razanhmede/Sorting_Conveyer_Belt_System/MEE341 - Project Submission/MEE341 - Project Submission/Mechanical Design 2/Gripper Assembly.SLDASM

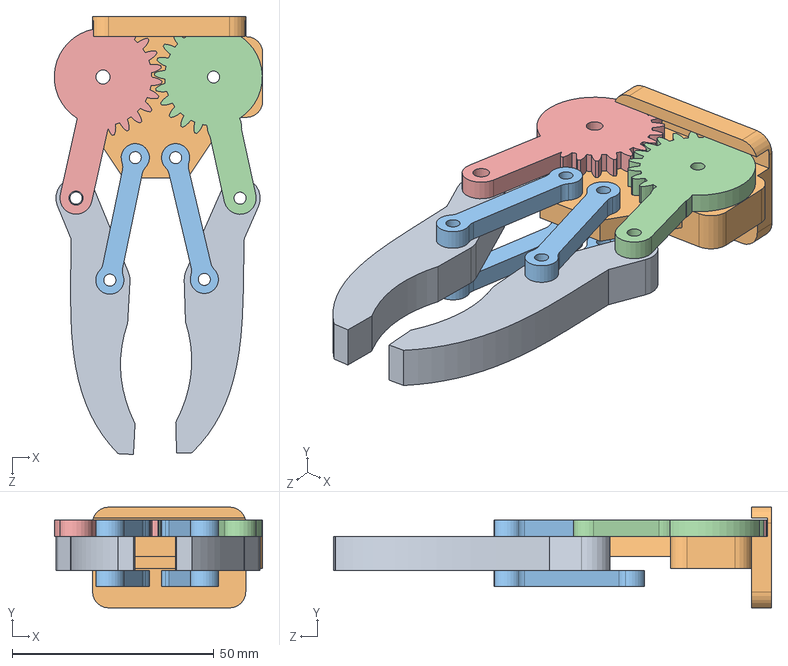
[picture p17: CAD file, 2024-09-03]
MEE341 - Project Submission/MEE341 - Project Submission/Mechanical Design 2/Gripper Assembly.SLDASM
51.7 x 25.0 x 108.6 mm
gear1
gear2
grip link 1 x 4
Gripper Base
Gripper 1 x 2
