razanhmede/Sorting_Conveyer_Belt_System/MEE341 - Project Submission/MEE341 - Project Submission/Mechanical Design 2/Robotic Arm Assembly.SLDASM

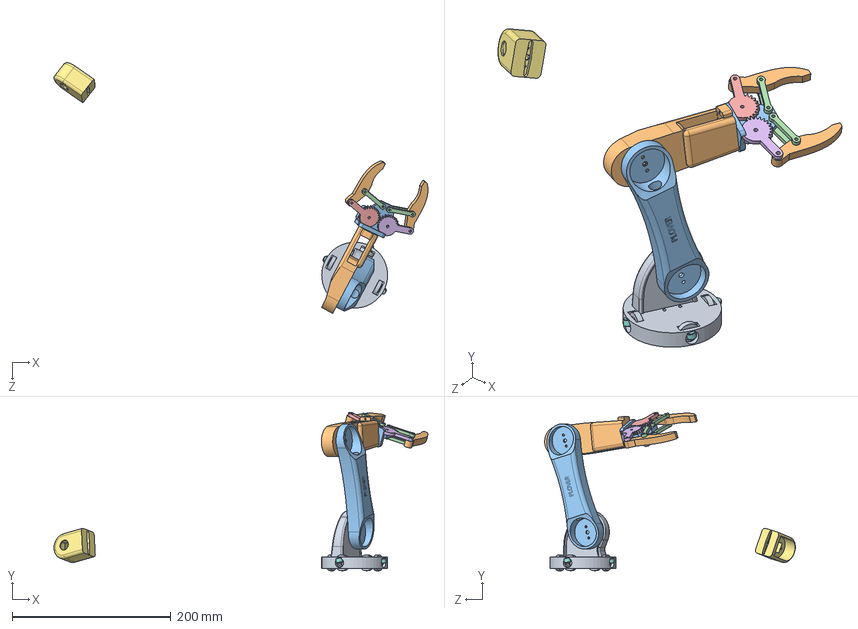
[picture p18: CAD file, 2024-09-03]
MEE341 - Project Submission/MEE341 - Project Submission/Mechanical Design 2/Robotic Arm Assembly.SLDASM
470.7 x 199.5 x 315.6 mm
Link 1
Link 2
Bearing x 4
Pin x 4
Link 3
gear1
gear2
grip link 1 x 4
Gripper Base
Gripper 1 x 2
Base Link - Copy
