razanhmede/Sorting_Conveyer_Belt_System/MEE341 - Project Submission/MEE341 - Project Submission/Mechanical Design 1/Pin.SLDPRT

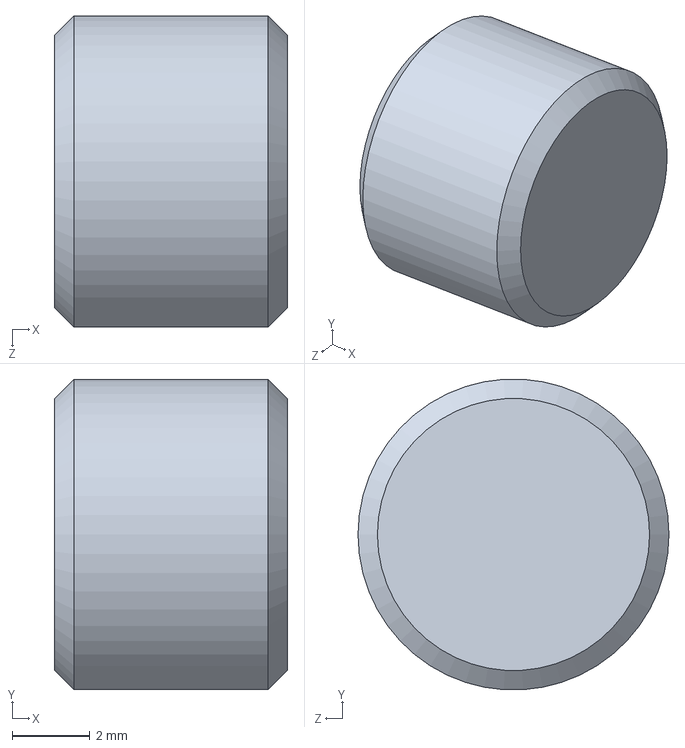
[picture p32: CAD file, 2024-09-03]
MEE341 - Project Submission/MEE341 - Project Submission/Mechanical Design 1/Pin.SLDPRT
6.00 x 7.98 x 8.00 mm
