razanhmede/Sorting_Conveyer_Belt_System/MEE341 - Project Submission/MEE341 - Project Submission/Mechanical Design 2/grip link 1_r1.SLDPRT

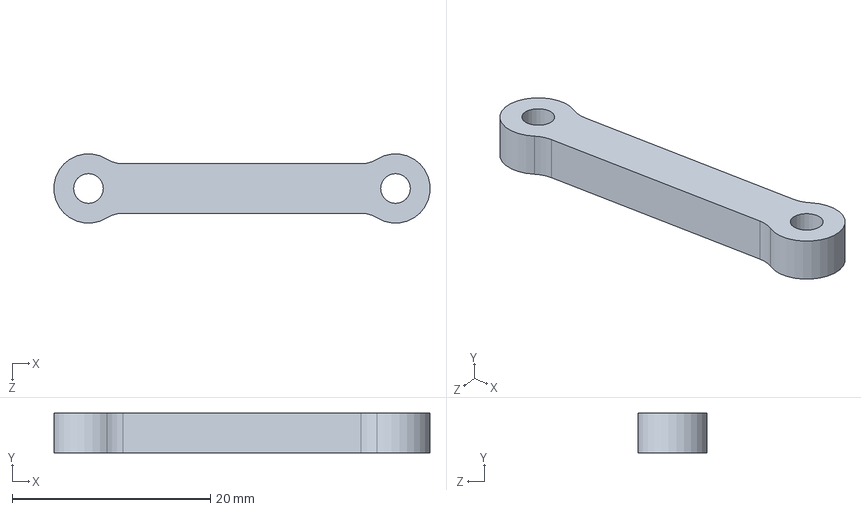
[picture p33: CAD file, 2024-09-03]
MEE341 - Project Submission/MEE341 - Project Submission/Mechanical Design 2/grip link 1_r1.SLDPRT
38.0 x 4.00 x 6.96 mm
