razanhmede/Sorting_Conveyer_Belt_System/MEE341 - Project Submission/MEE341 - Project Submission/Mechanical Design 1/Spacer.SLDPRT

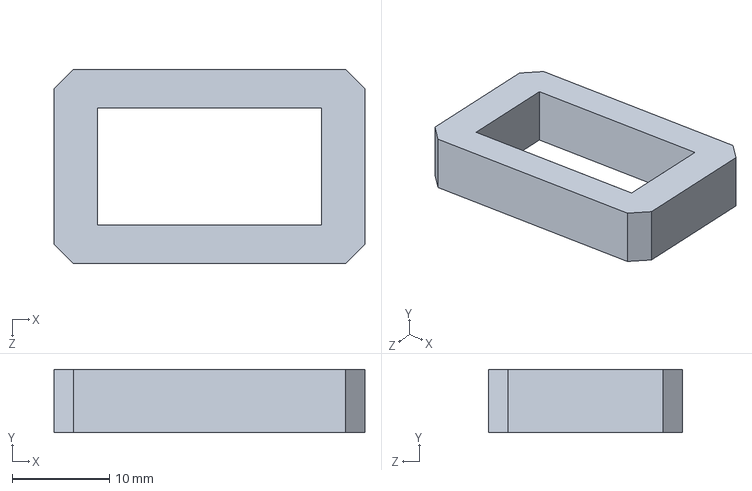
[picture p34: CAD file, 2024-09-03]
MEE341 - Project Submission/MEE341 - Project Submission/Mechanical Design 1/Spacer.SLDPRT
32.0 x 6.50 x 20.0 mm
