razanhmede/Sorting_Conveyer_Belt_System/MEE341 - Project Submission/MEE341 - Project Submission/Mechanical Design 1/spacer.STL.SLDPRT

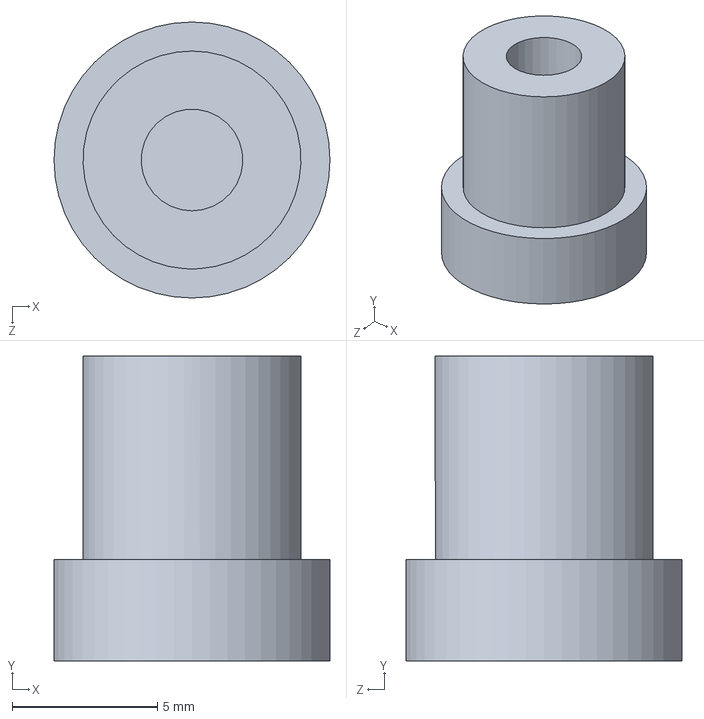
[picture p35: CAD file, 2024-09-03]
MEE341 - Project Submission/MEE341 - Project Submission/Mechanical Design 1/spacer.STL.SLDPRT
9.50 x 10.5 x 9.50 mm
