razanhmede/Sorting_Conveyer_Belt_System/MEE341 - Project Submission/MEE341 - Project Submission/Mechanical Design 2/Gripper 1.SLDPRT

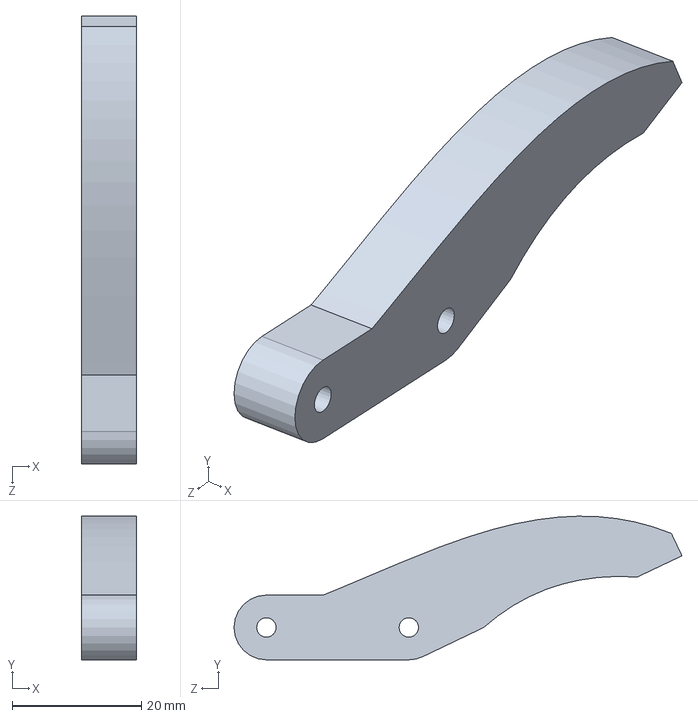
[picture p36: CAD file, 2024-09-03]
MEE341 - Project Submission/MEE341 - Project Submission/Mechanical Design 2/Gripper 1.SLDPRT
8.50 x 22.2 x 69.2 mm
