razanhmede/Sorting_Conveyer_Belt_System/MEE341 - Project Submission/MEE341 - Project Submission/Mechanical Design 2/Pin.SLDPRT

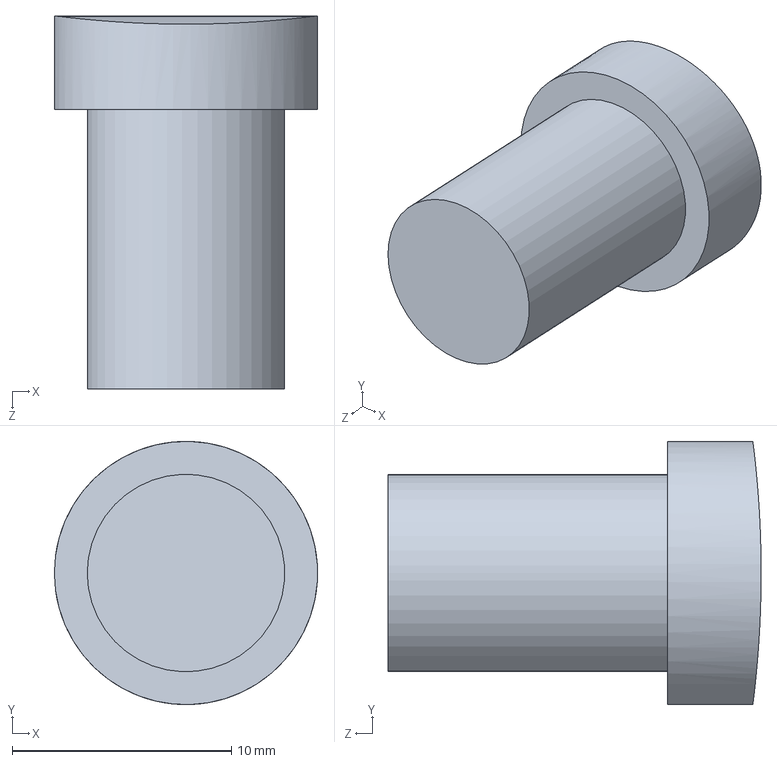
[picture p37: CAD file, 2024-09-03]
MEE341 - Project Submission/MEE341 - Project Submission/Mechanical Design 2/Pin.SLDPRT
12.0 x 12.0 x 17.0 mm
