razanhmede/Sorting_Conveyer_Belt_System/MEE341 - Project Submission/MEE341 - Project Submission/Mechanical Design 2/Gripper Base.SLDPRT

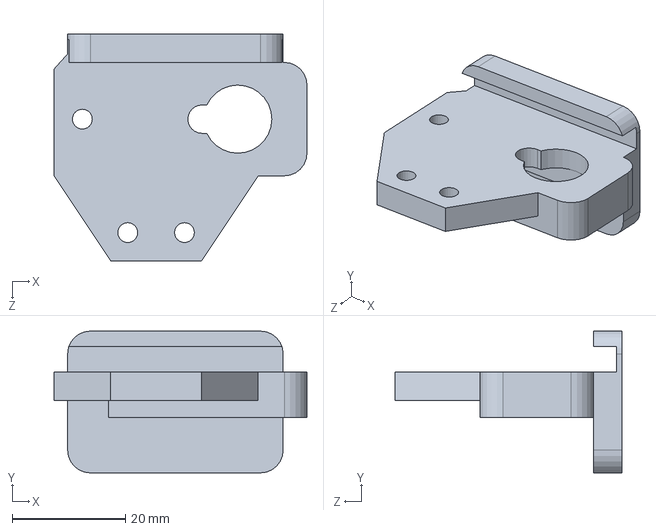
[picture p38: CAD file, 2024-09-03]
MEE341 - Project Submission/MEE341 - Project Submission/Mechanical Design 2/Gripper Base.SLDPRT
44.6 x 25.0 x 40.0 mm
