razanhmede/Sorting_Conveyer_Belt_System/MEE341 - Project Submission/MEE341 - Project Submission/Mechanical Design 2/Link 2.SLDPRT

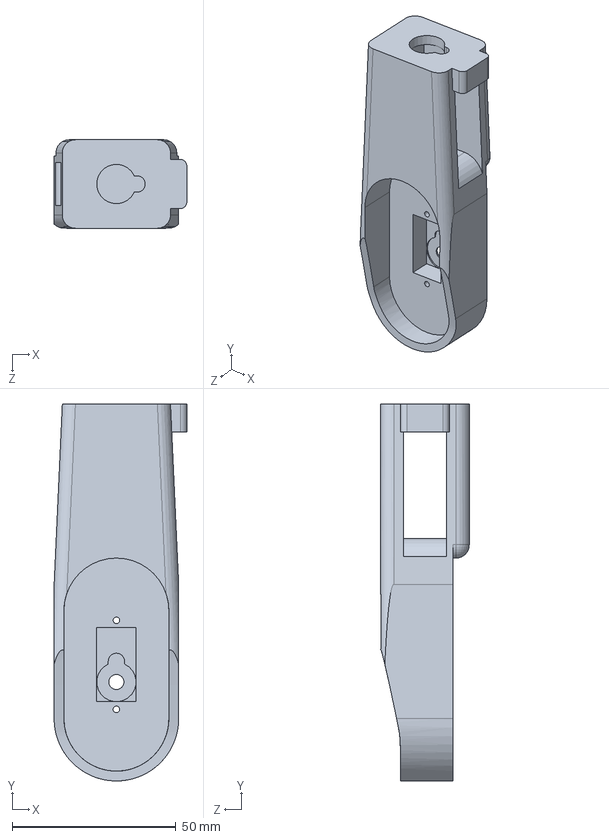
[picture p39: CAD file, 2024-09-03]
MEE341 - Project Submission/MEE341 - Project Submission/Mechanical Design 2/Link 2.SLDPRT
40.5 x 115.0 x 27.0 mm
