razanhmede/Sorting_Conveyer_Belt_System/MEE341 - Project Submission/MEE341 - Project Submission/Mechanical Design 2/gear1.SLDPRT

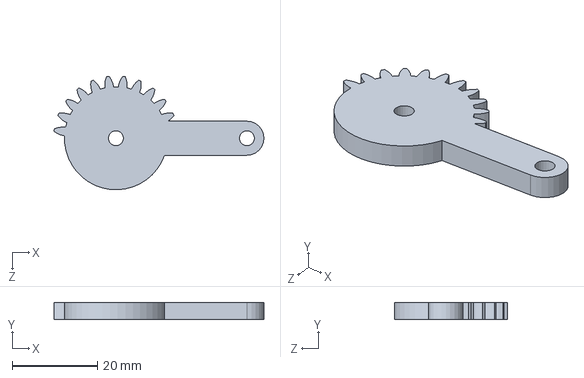
[picture p40: CAD file, 2024-09-03]
MEE341 - Project Submission/MEE341 - Project Submission/Mechanical Design 2/gear1.SLDPRT
49.3 x 4.00 x 26.6 mm
