razanhmede/Sorting_Conveyer_Belt_System/MEE341 - Project Submission/MEE341 - Project Submission/Mechanical Design 2/Bearing.SLDPRT

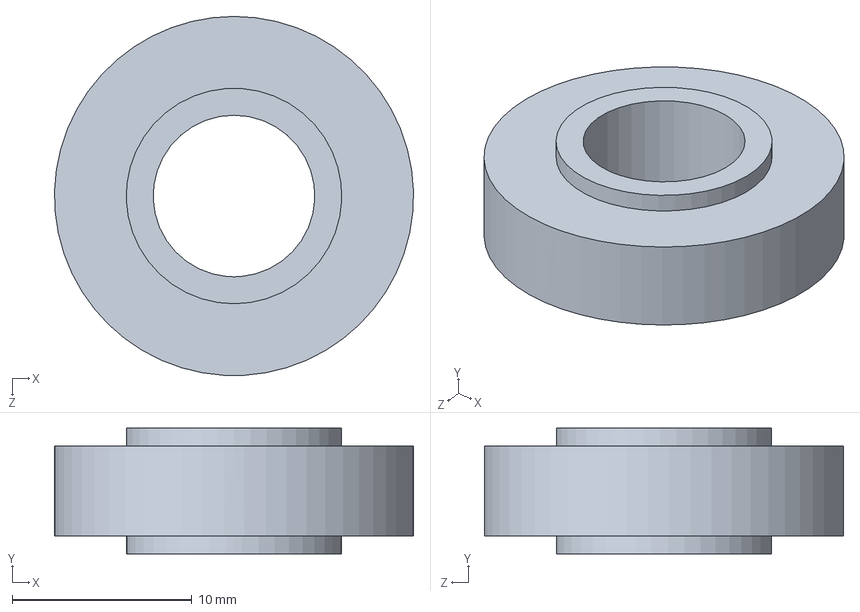
[picture p41: CAD file, 2024-09-03]
MEE341 - Project Submission/MEE341 - Project Submission/Mechanical Design 2/Bearing.SLDPRT
20.0 x 7.00 x 20.0 mm
