razanhmede/Sorting_Conveyer_Belt_System/MEE341 - Project Submission/MEE341 - Project Submission/Mechanical Design 2/Motor Base.SLDPRT

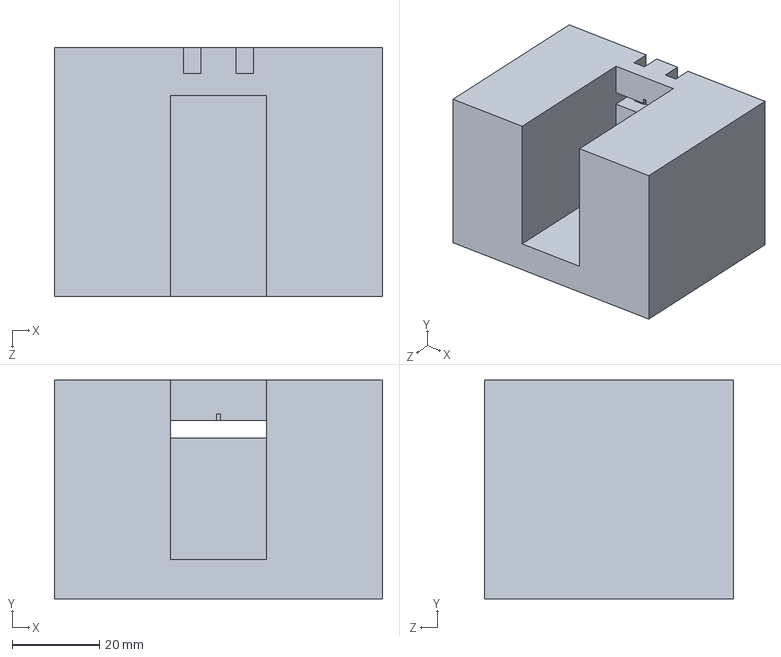
[picture p42: CAD file, 2024-09-03]
MEE341 - Project Submission/MEE341 - Project Submission/Mechanical Design 2/Motor Base.SLDPRT
75.0 x 50.0 x 57.0 mm
