razanhmede/Sorting_Conveyer_Belt_System/MEE341 - Project Submission/MEE341 - Project Submission/Mechanical Design 2/gear2.SLDPRT

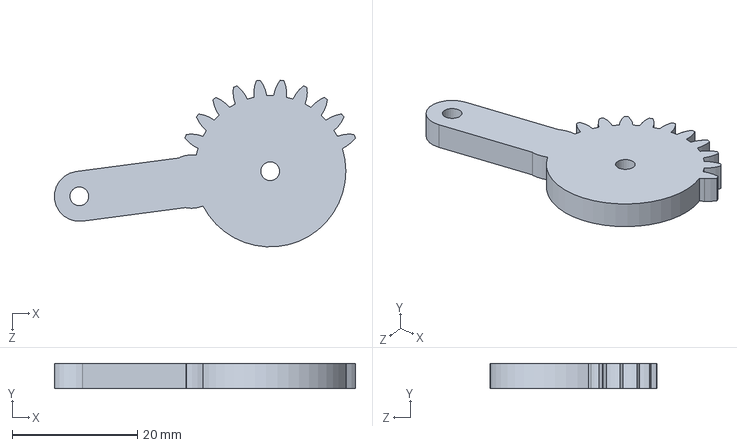
[picture p43: CAD file, 2024-09-03]
MEE341 - Project Submission/MEE341 - Project Submission/Mechanical Design 2/gear2.SLDPRT
48.1 x 4.00 x 26.6 mm
